shyver/Precision-Light-Sensor-AFE/media/pcb_3d_ortho.png

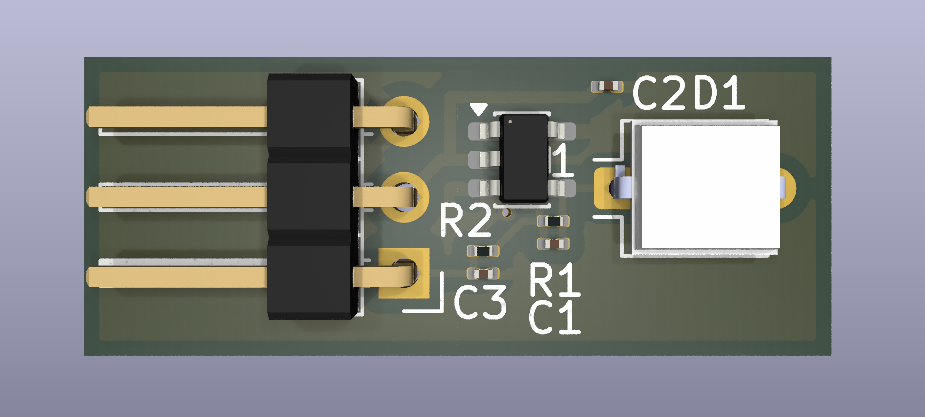
media/pcb_3d_ortho.png
