shyver/Precision-Light-Sensor-AFE/media/pcb_back.png

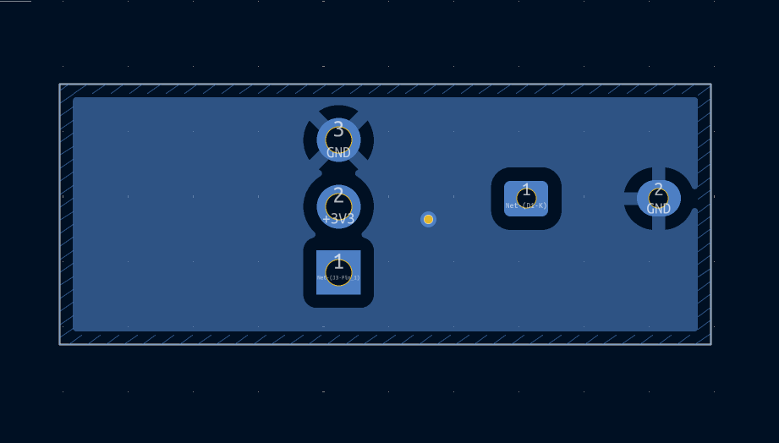
media/pcb_back.png
