shyver/Precision-Light-Sensor-AFE/media/transient response (uncompensated).png

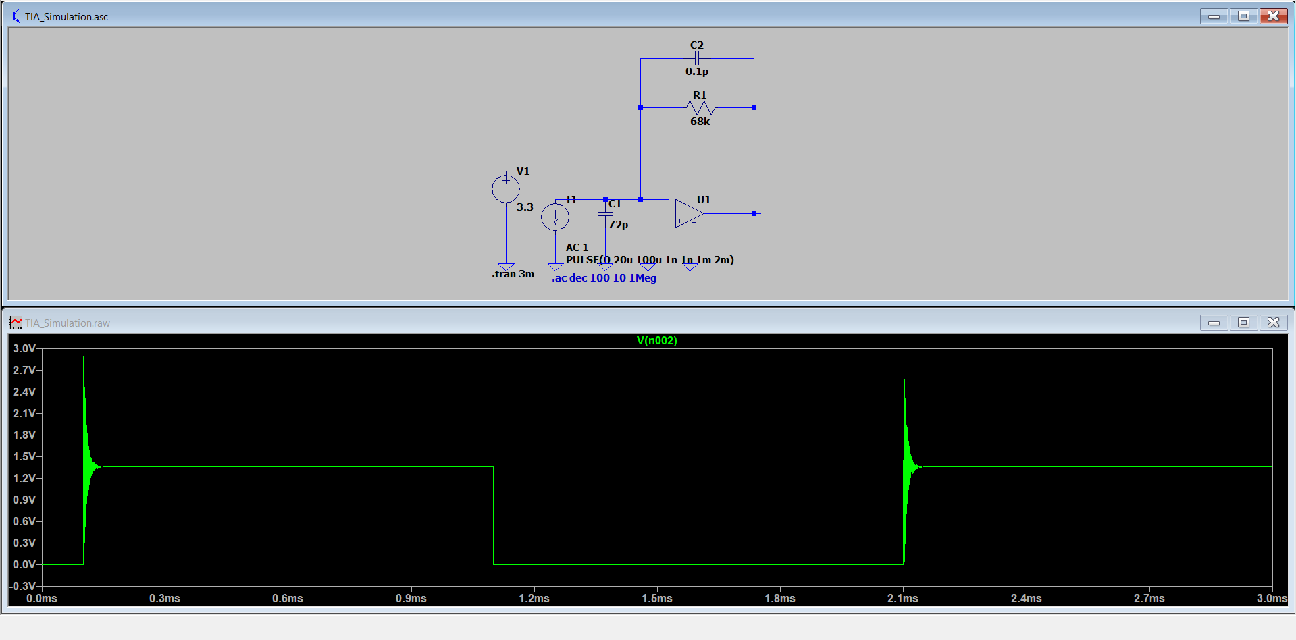
media/transient response (uncompensated).png
