shyver/Precision-Light-Sensor-AFE/simulation/TIA_Simulation.asc

C1: cap; 72p
C2: cap; 20p
I1: current; PULSE(0 20u 100u 1n 1n 1m 2m); AC 1
R1: res; 68k
U1: UniversalOpAmp2
V1: voltage; 3.3
Named nets: 0
.tran 3m
.ac dec 100 10 1Meg
